Makerfabs/4G-LTE-Hat-For-Raspberry-Pi/md_pic/connectarduino.jpg

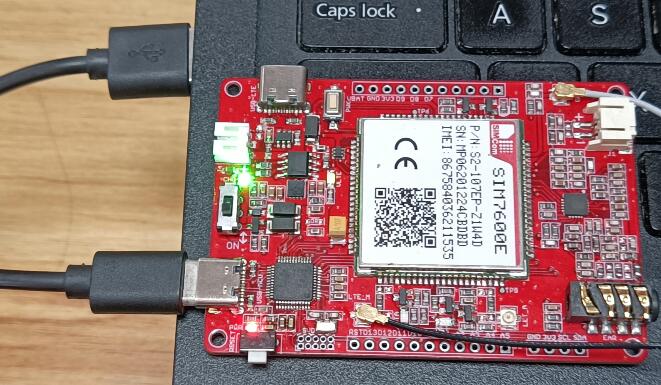
md_pic/connectarduino.jpg
