Makerfabs/4G-LTE-Hat-For-Raspberry-Pi/md_pic/dht11.jpg

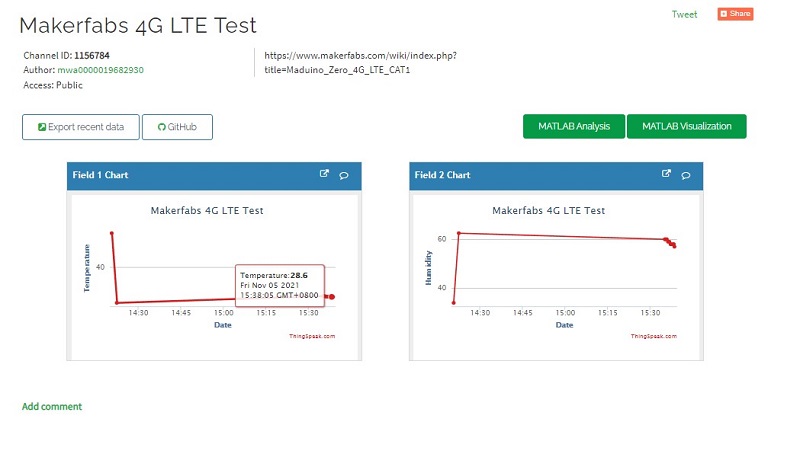
md_pic/dht11.jpg
